artiompujleacov/Proiectsc/Images/2.png

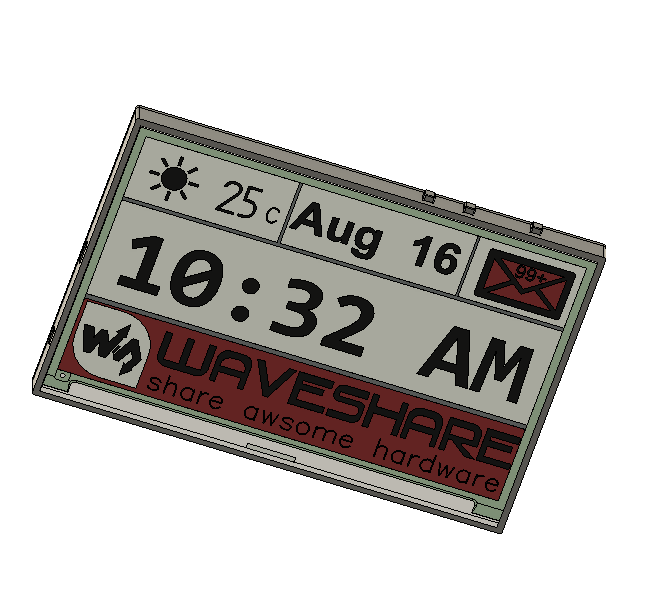
Images/2.png
