artiompujleacov/Proiectsc/Images/3.png

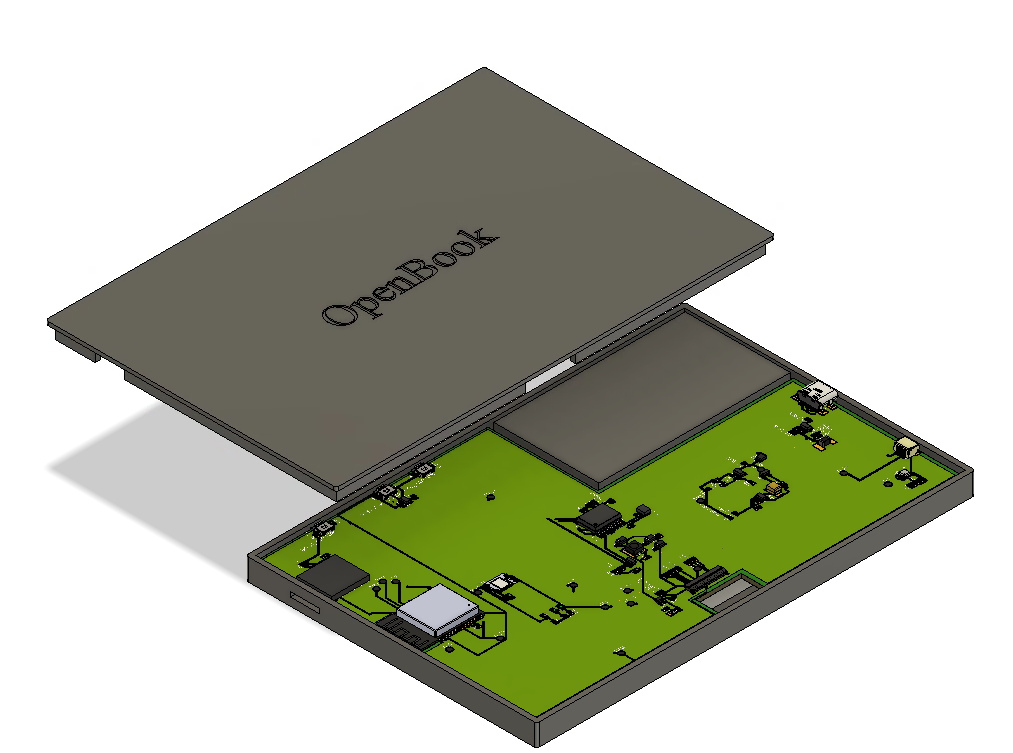
Images/3.png
